AnnieL5/ThermoBuzzer/docs/images/image-3.png

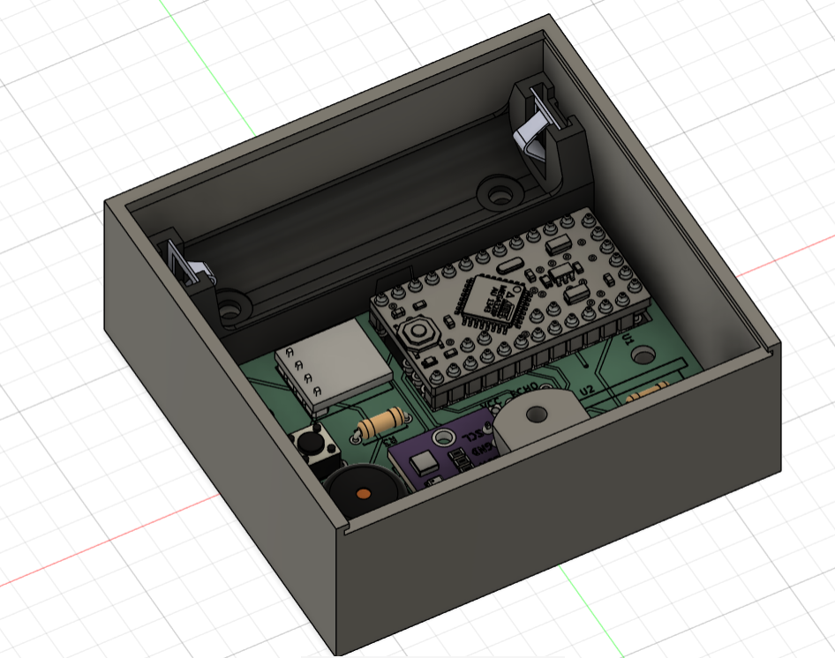
docs/images/image-3.png
