AnnieL5/ThermoBuzzer/docs/images/image-4.png

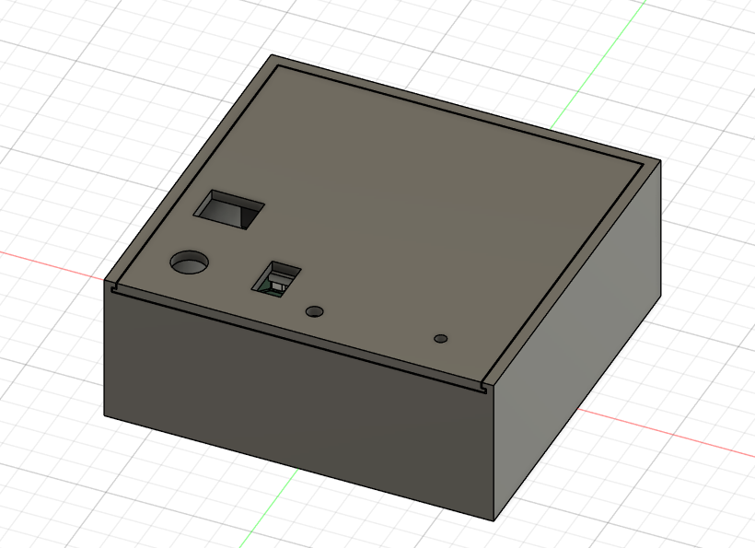
docs/images/image-4.png
